HayaAbusada/The-Wranglers/Reports/Weekly Report #6.pdf

WEEKLY REPORT and MEETING AGENDA

Report #: | 6 | Project Name: Car Rider Pickup System for Schools
Date: | 4/13/2026 | Prepared by: All Team Members

Agenda for the meeting

### 1. First 3D print 2. Server setup and fully working

3.
4.
5.

Overall accomplishments since last meeting

### 1. First housing model printed - revisions need to be made 2. Server connection working 3. Zigbee infrastructure and configuration complete

4.
5.

Tasks completed by each team member since last meeting

Task description | Assigned to | Completed?
Start implementing Zigbee connections between all modules | Jake | Yes
Coding server to camera connection | Haya | No
Coding server to database connections | Sara | No
Finished Zigbee setup and establish communications | Jack | Yes
Get final housing design printed | Jayden | Yes

Plans for next period

### 1. Put together system prototype (all parts + 3d print print) 2. Fix UI with server connection on website 3. Finish server to database connection 4. Finish server to camera connection 5. Complete Pi software and networking(Zigbee)

Task assignment per team member (to be completed before the next meeting)

Task description | Assigned to
Put together system prototype (all parts + 3d print print) | Jayden
Fix UI with server connection on website | Haya
Finish server to database connection | Sara
Finish server to camera connection | Jake
Complete Pi software and networking(Zigbee) | Jack

Weekly Report Form. CSCE 483 Computer System Design

Project management status

### 1. Our project is running on time according to our Monday board

2.
3.

Minutes from previous meeting
-Decide on singular method - (QR code) -

Weekly Report Form. CSCE 483 Computer System Design
