HayaAbusada/The-Wranglers/Reports/Weekly Report #7.pdf

WEEKLY REPORT and MEETING AGENDA

Report #: | 7 | Project Name: Car Rider Pickup System for Schools
Date: | 4/22/2026 | Prepared by: All Team Members

Agenda for the meeting

### 1. Demo Complete Project

2.
3.
4.
5.

Overall accomplishments since last meeting

### 1. Housing model printed and assembled 2. All modules communicating over WiFi 3. Full System functionality

4.
5.

Tasks completed by each team member since last meeting

Task description | Assigned to | Completed?
Put together system prototype (all parts + 3d print print) | Jayden | Yes
Fix UI with server connection on website | Haya | Yes
Finish server to database connection | Sara | Yes
Finish server to camera connection | Jake | Yes
Complete Pi software and communication | Jack | Yes

Plans for next period

### 1. Write User Manual and implementation notes 2. Produce final report, presentation and deliverables

3.
4.
5.

Task assignment per team member (to be completed before the next meeting)

Task description | Assigned to
Put together Final Documentation, Report and Presentation | Everyone

Weekly Report Form. CSCE 483 Computer System Design

Project management status

### 1. Our project is running on time according to our Monday board - Completed

2.
3.

Minutes from previous meeting

Weekly Report Form. CSCE 483 Computer System Design
