HayaAbusada/The-Wranglers/Audiovisual_Media/Video Demo.pdf

Can’t Upload to Git – Here is Video Demo: https://drive.google.com/file/d/1vi21LkvK88VlowLp8_o5fa8o9luOnCKN/view?usp=sharing
